ph-design/PH60/Case_Model_Rev3/stand.step

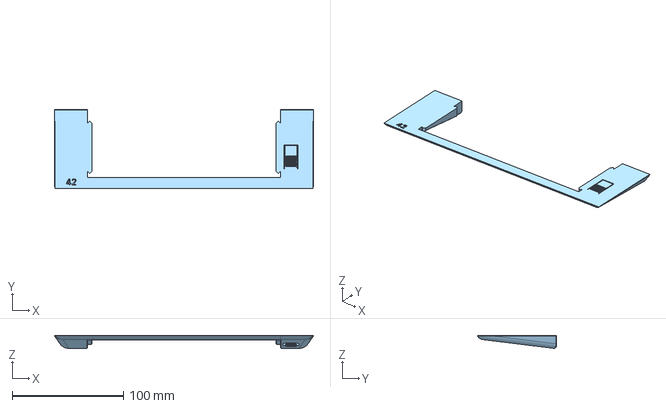
[picture p18: CAD file, 2026-04-19]
Case_Model_Rev3/stand.step
233.3 x 71.4 x 11.6 mm
