ph-design/PH60/Case_Model_Rev3/outer_case_hhkb_6u_split_b.step

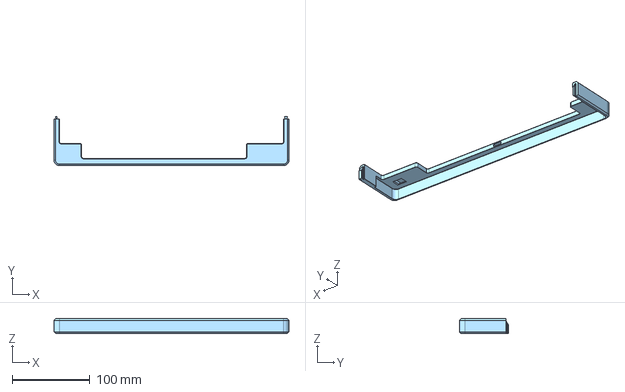
[picture p19: CAD file, 2026-04-19]
Case_Model_Rev3/outer_case_hhkb_6u_split_b.step
301.4 x 63.3 x 18.7 mm
plate
main_frame
