ph-design/PH60/Case_Model_Rev3/magnet_drawer.step

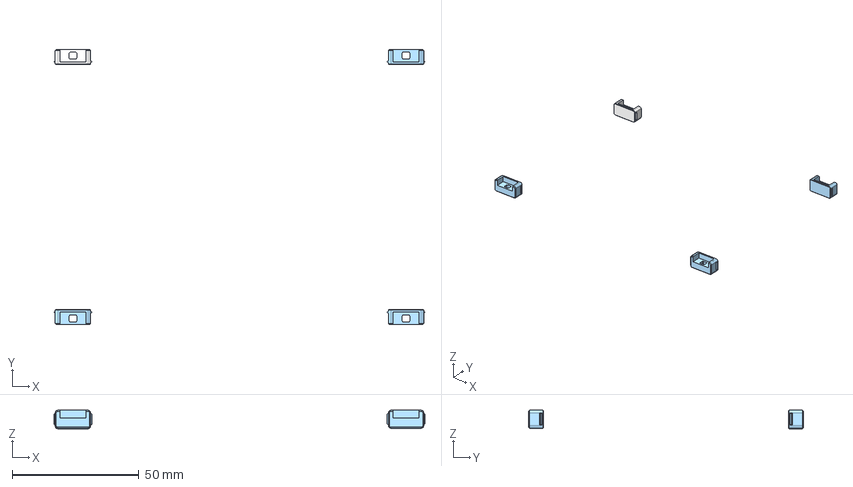
[picture p20: CAD file, 2026-04-19]
Case_Model_Rev3/magnet_drawer.step
146.2 x 108.5 x 7.30 mm
