ph-design/PH60/Case_Model_Rev3/inner_case_right.step

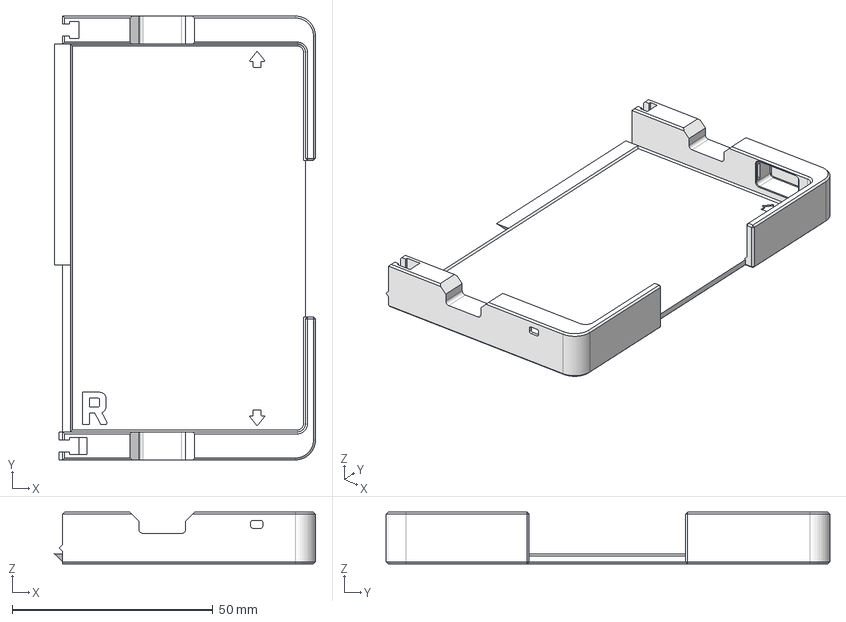
[picture p21: CAD file, 2026-04-19]
Case_Model_Rev3/inner_case_right.step
65.0 x 110.5 x 12.9 mm
