ph-design/PH60/Case_Model_Rev3/inner_case_damp.step

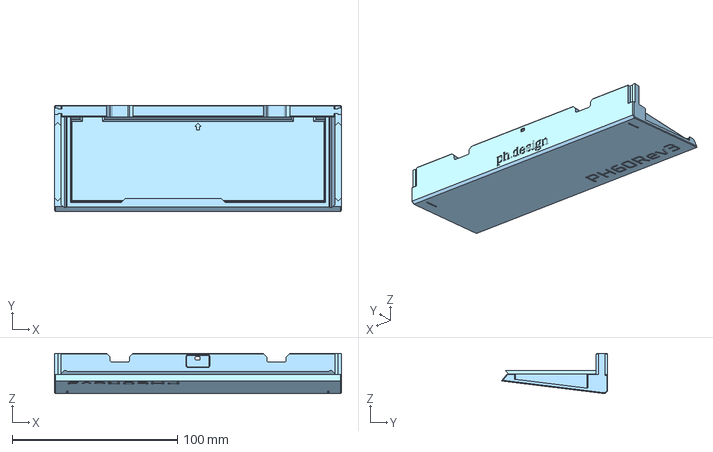
[picture p22: CAD file, 2026-04-19]
Case_Model_Rev3/inner_case_damp.step
173.7 x 64.5 x 24.4 mm
